CedarGroveStudios/PCB_Reintegrator/media/IMG_0337.jpg

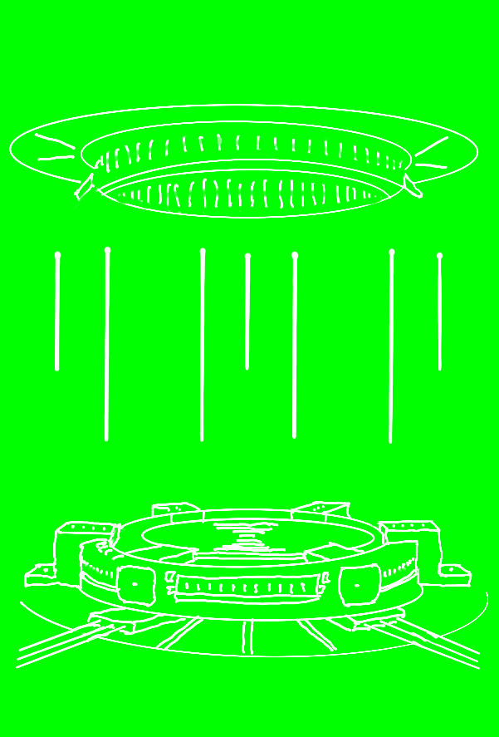
media/IMG_0337.jpg
